Ocsof/smart-radar/src/arduino/smart-cm/Scheduler.h

#ifndef __SCHEDULER__
#define __SCHEDULER__

#include "Timer.h"
#include "Task.h"

#define MAX_TASKS 15

class Scheduler {
  int basePeriod;
  int nTasks;
  Task* taskList[MAX_TASKS];  
  Timer timer;

public:
  void init(int basePeriod);  
  virtual bool addTask(Task* task);  
  virtual void schedule();
};

#endif
