Ocsof/smart-radar/src/arduino/smart-cm/PotentiometerImpl.cpp

#include "PotentiometerImpl.h"
#include "Arduino.h"

PotentiometerImpl::PotentiometerImpl(int analogInPin){
    this->analogInPin= analogInPin;
}

int PotentiometerImpl::getValue(){
    return analogRead(analogInPin);
}
